ArielleZhang/ESC204_PraxisIII_The_wandering_sheep/Design Pitch Artefacts/Design Consideration and Prototyping Artefacts/Phase B/Database + UI/grassresized.png

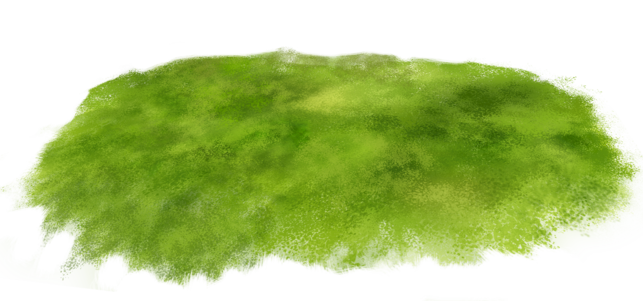
Design Pitch Artefacts/Design Consideration and Prototyping Artefacts/Phase B/Database + UI/grassresized.png
