ArielleZhang/ESC204_PraxisIII_The_wandering_sheep/Design Milestones/Prototype/Physical Collar Design/DesignOutline.docx

Belt

1. Use vinyl for the belt, this is waterproof and durable, an ideal material for sheep collar.(remember to sandpaper the edge to avoid sharp edges)
2. Belt buckles, 3D print two square rings. (from reference design, this is easier to use compared to watch style belts with complicated buckles)

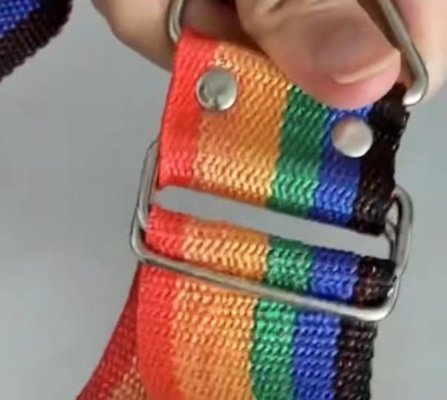
[picture p41: figure]

3. Belt case connections: still need to think about how to attach the belts onto the case. There are two ear rings on the case.

Case:

1. Size is 72mmx62mmx20mm right now. (Could we make it even smaller?)
2. Need to hold the Arduino and the Bluefruit in place, no movements even when shaking.
  a. Add a middle layer for the Bluefruit, need to drill holes and screw it on the plate.
3. Waterproof/dustproof mechanism.
