ArielleZhang/ESC204_PraxisIII_The_wandering_sheep/Design Milestones/Phase A/To Do.docx

- Executive summary – write when finished
- Finish up opportunity statement (confusing) - write when finished
- Background (Ethan was working on this)
- Reference design (fencing) (Ethan)
- Team value proposition - Edwin
- Individual requirements write up (make it into paragraph form, follow cost-efficiency format)
- Emre's team description
- Everything design related:
  - Finalizing the two designs (Arielle&Tab&Edwin work on one design, Emre&Ethan work on the other design)
  - Design descriptions
    - Thermal
    - Image recognition
  - Prototype for thermal (or whatever we’re choosing)
  - why the second one didn’t work
- Project management plan summary (Arielle)
