ArielleZhang/ESC204_PraxisIII_The_wandering_sheep/Design Pitch Artefacts/Project Management Artefacts/3. Communication Protocol.docx

Communication Protocol Be responsive: - Keep up with messages in group chats (discord) regularly and reply ASAP Show punctuality: - Don’t be late, have time strictly reserved for Praxis! Be communicative: - Come prepared to all meetings - Speak up/ don’t be shy, no one is judging - Contribute ideas to the group Be attentive and respectful: - Keep an open mind to everyone's opinions - Try to think in each other's perspectives
