ArielleZhang/ESC204_PraxisIII_The_wandering_sheep/Housekeeping/GSU_Interaction/GSU Initial Contact.docx

Initial contact with the GSU student

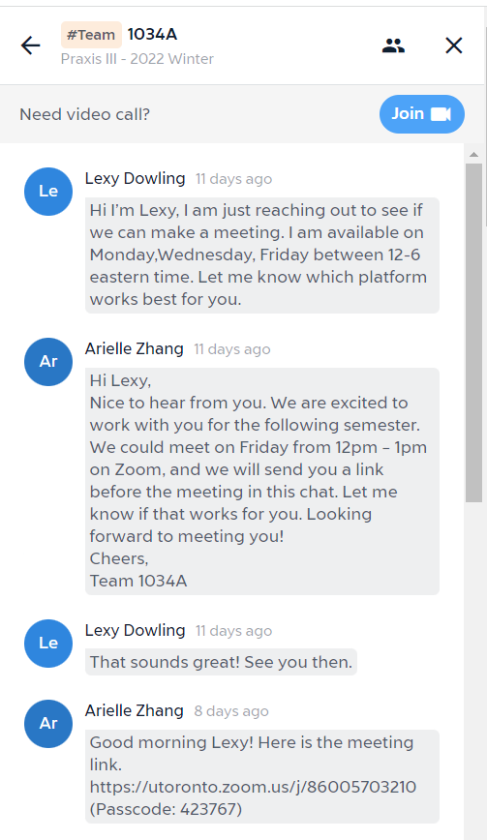
[picture p56: figure]
