ArielleZhang/ESC204_PraxisIII_The_wandering_sheep/Housekeeping/GSU_Interaction/GSU meeting confirmation.docx

GSU Meeting Confirmation Email

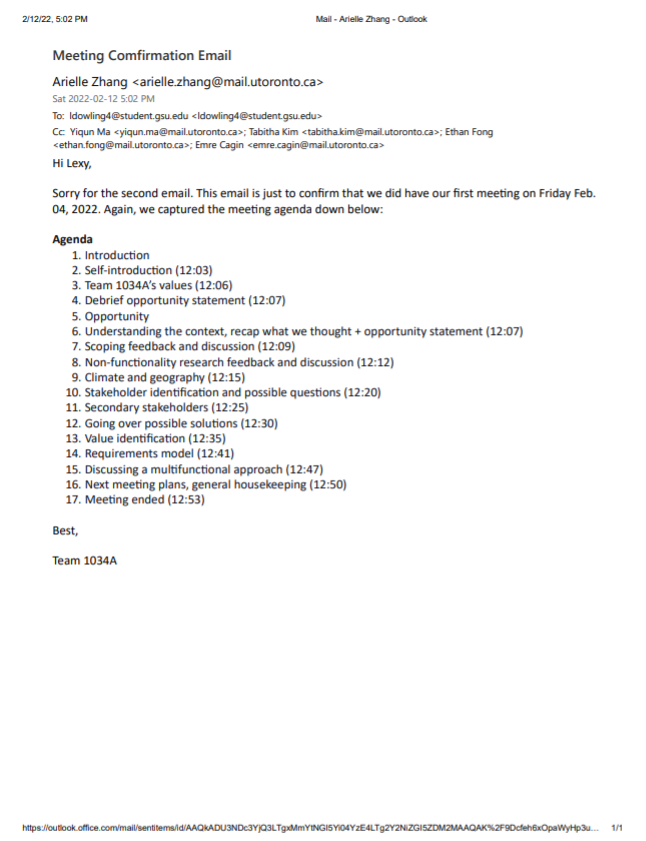
[picture p57: figure]
