ArielleZhang/ESC204_PraxisIII_The_wandering_sheep/Research/Yiqn_Research/Solution.docx

Edwin Research

Possible solution

Drone Method

The drone is efficient and easy to control, the controller is designed to be as much easy as we can. The drone is small and fast that can fly everywhere, sheep can only wander off around 5km, so using drones to find where they are is much easier for owners to drive cars to each one’s house. Drones can also be used as monitors, both check the actions of shepherds and chase for missing sheep at the first second they wander off, this increases the efficiency for the owner to find back their sheep since they know exactly where to go.

The drone can be also used to monitor situations of sheep in the crowd, for example, the new birth is produced, the owner can know the message immediately as they can see all the scenes of his sheep. Thermal imaging is another key feature to monitor the health of sheep.

Sensors can be used to identify belong of the sheep, the paint on sheep will affect the wool production, so I think an induction device placed on sheep’s ear that can produce certain signals can solve the problem of identifying sheep. All families on this land can select their signals for drones to identify the owner of lost sheep.

Ease of learning

an individual’s prediction of how easy it will be to acquire and retain certain items of information, given before any attempt is made to do so. In tests of learning and memory, participants’ pretest ease-of-learning judgments tend to be only weakly correlated with their performance on the test. Like the feeling of knowing (https://dictionary.apa.org/feeling-of-knowing), ease-of-learning judgments are an important aspect of metacognition (https://dictionary.apa.org/metacognition). Compare retrospective confidence judgment (https://dictionary.apa.org/retrospective-confidence-judgment).

The two methods of drone and tracker are both easy for them to learn, it is easy to put the tracker on sheep’s ears and use their phone to track their locations. Also it will only take a short time to learn how to use the drones
