ArielleZhang/ESC204_PraxisIII_The_wandering_sheep/Design Pitch Artefacts/Project Management Artefacts/ESC204S-Course-Schedule-Gantt-Chart-2022-STUDENT-COPY.xlsx

Sheet: Schedule Gantt - Mostly Phase A
Month | January |  |  | February |  |  |  | March |  |  |  | April
Week | WK 1 | WK 2 | WK 3 | WK 4 | WK 5 | WK 6 | WK 7 | WK 8 | WK 9 | WK 10 | WK 11 | WK 12 | WK 13 | WK 14 | Exam Period
Dates | 01/10 - 01/16 | 01/17 - 01/23 | 01/24 - 01/30 | 01/31 - 02/06 | 02/07 - 02/13 | 02/14 - 02/20 | 02/21 - 02/27 | 02/28 - 03/06 | 03/07 - 03/13 | 03/14 - 03/20 | 03/21 - 03/27 | 03/28 - 04/03 | 04/04 - 04/10 | 04/11 - 04/16 | 04/19 - 04/23 | 04/24 - 04/30
Deliverable / Activity
Meeting |  |  |  |  |  |  |  |  | Meeting 1 | No Merting, update through DC
Studios |  |  |  |  |  |  |  |  | Studio A: 1. TELS 2. Prototype, checkin with the team resiponsibility tracker 3. Widget Lab 3 order | Studio B: 1. continue debugging GPS 2. finish lab 3 code+cad 3. procurement Studio A: 1. Start on prototype 2. Budget upadte 3. start on widet lab 3 4. lab3 report | Studio A: 1. TELS 2.Prototype 3. Requirements + testing protocol | Studio A 1. Follower sheep assembling 2. Backend read from serial monitor, UI 3. Brochure 4. Testing protocol | Presentation on Friday | Documeny + demo due
Design Pitch |  |  |  |  |  |  |  |  | 2021-03-07 |  |  |  |  | 2022-04-17
PMP Review |  |  |  |  |  |  |  |  |  | Studio B
Prototyping Check-In |  |  |  |  |  |  |  |  | 2021-03-07 |  | Studio B
Design Pitch Brochure |  |  |  |  |  |  |  |  | 2021-03-07 |  |  | 2022-04-03
Deign Pitch Presentation + Recordings |  |  |  |  |  |  |  |  | 2021-03-07 |  |  |  | Studio A+B
Design Pitch Document & Prototype Demo Recordings |  |  |  |  |  |  |  |  | 2021-03-07 |  |  |  |  | 2021-04-17
GSU Peer Interactions
GSU Peer Interactions - Phase A - Synchronous Meeting (https://q.utoronto.ca/courses/244355/assignments/806370) |  |  |  | 2021-01-31 | 2022-02-13
GSU Peer Interactions - Phase B - Asynchronous Feedback |  |  |  |  |  |  |  | 2021-03-06 | 2022-03-13
Reflections (Individual Designer's Identity)
Reflection 1 - Designer's Empathy (https://q.utoronto.ca/courses/244355/assignments/794634) | 2022-01-13 | 2021-01-23
Reflection 2 - Designer's Bias |  |  |  |  |  |  |  |  | 2022-03-08 | 2022-03-20
Refleciton 3 |  |  |  |  |  |  |  |  |  |  |  |  | 2021-04-04 |  | 2021-04-23
TELS
TELS 1 |  |  |  |  |  |  |  | 2022-03-01 | 2021-03-13
TELS 2 |  |  |  |  |  |  |  |  |  |  |  |  |  | TBD | 2021-04-23
Team Video Recordings
Team Meeting Video Recording - Phase A (https://q.utoronto.ca/courses/244355/assignments/820351) |  | Studio A |  |  |  |  |  | 2021-03-06
Team Meeting Video Recording - Phase B |  |  |  |  |  |  |  |  | 2021-03-07 |  |  |  |  |  |  | 2021-04-30
Widget Skill Building
Lab 1 - Basic Systems Prototyping (pairs) (https://q.utoronto.ca/courses/244355/assignments/797602) | 2022-01-16 |  |  | 2022-02-06
Lab 2 - Intermediate Systems Prototyping (teams) (https://q.utoronto.ca/courses/244355/assignments/816949) |  |  |  |  | 2022-02-07 |  |  |  | 2022-03-09
Lab 3 - Advanced Systems Prototyping (teams) |  |  |  |  |  |  |  | 2022-03-04 |  |  | 2022-03-23
Design Proposal Process (https://q.utoronto.ca/courses/244355/assignments/818248) | 2022-01-12 |  |  |  |  | 2021-02-20
Project Framing |  |  | 2022-01-24 | Studio A |  | 2021-02-20
Design Considerations |  |  | 2022-01-24 |  | Studio A | 2021-02-20
Project Management Plan |  | Studio A | Studio A | Studio A | Studio A | 2021-02-20
Course Introduction & Setup
Survey & Team Formation (https://q.utoronto.ca/courses/244355/assignments/793460) | 01/12-01/15
Legend
begin / assigned | M/DD | Studio A or B
in-progress
submission due 23:59 ET (unless otherwise specified) | M/DD
informal (in-studio) check-in on current state | Studio A or B
submission not assessed (used for course improvement) | M/DD
deadline for external partners (nothing to submit) | M/DD

Sheet: Weekly Timetable
Time | Monday | Tuesday |  |  |  |  | Wednesday |  | Thursday |  |  |  |  |  | Friday
9:00:00 |  |  |  |  |  |  |  |  |  |  | TUT0109 | TUT0110 | TUT0107 | TUT0108 | PRA0103 | PRA0104 | PRA0109 | PRA0110 | PRA0107 | TUT0108
10:00:00 |  |  |  |  |  |  |  |  | PRA0111 | PRA0112
11:00:00
12:00:00 |  | PHILIP IN CAPSTONE
13:00:00 |  |  |  |  |  |  | TUT0111 | TUT0112 | PRA0101 | PRA0102
14:00:00 |  |  |  |  |  |  |  |  |  |  | PRA0105 | PRA0106 |  |  | LEC
15:00:00 |  |  | TUT0101 | TUT0102 | TUT0105 | TUT0106 | TUT0103 | TUT0104 | PHILIP IN |  |  |  | CAPSTONE
16:00:00 | LEC
17:00:00 |  | LEC
18:00:00 |  | TUT0113 |  |  |  |  |  |  | PRA0113
19:00:00
20:00:00
