ArielleZhang/ESC204_PraxisIII_The_wandering_sheep/Design Milestones/Prototype/Back End/First Version/shaun.png

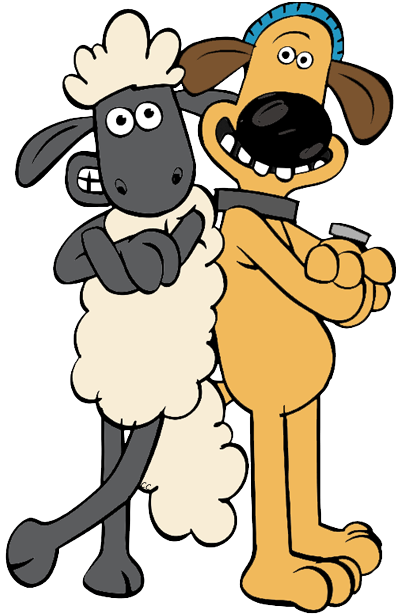
Design Milestones/Prototype/Back End/First Version/shaun.png
