ArielleZhang/ESC204_PraxisIII_The_wandering_sheep/Design Milestones/Prototype/Conceptual Design.png

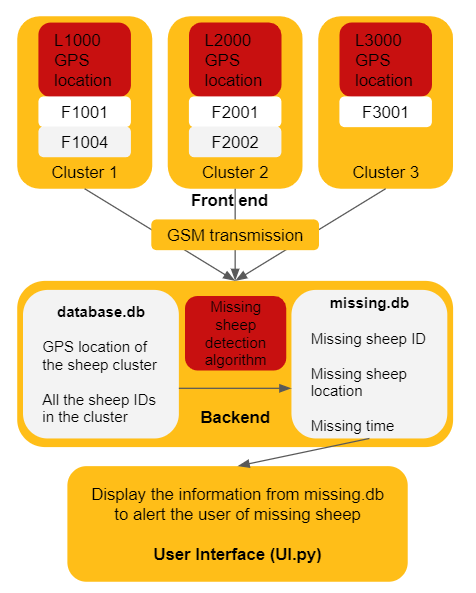
Design Milestones/Prototype/Conceptual Design.png
