ArielleZhang/ESC204_PraxisIII_The_wandering_sheep/Design Milestones/Prototype/green design concept.png

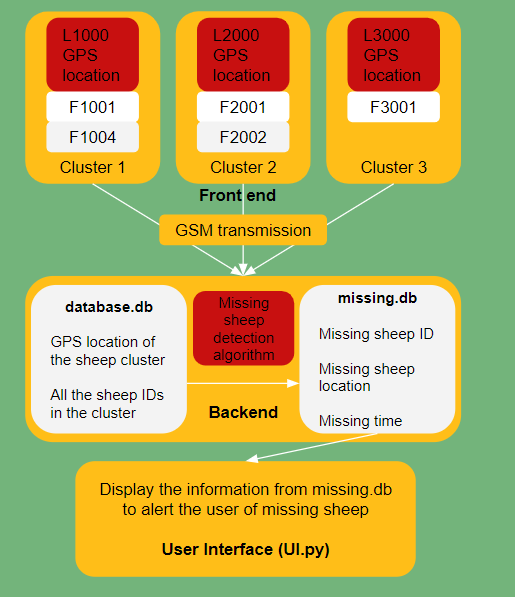
Design Milestones/Prototype/green design concept.png
