ArielleZhang/ESC204_PraxisIII_The_wandering_sheep/Design Milestones/Prototype/Physical Collar Design/Collar_Design_Version1.png

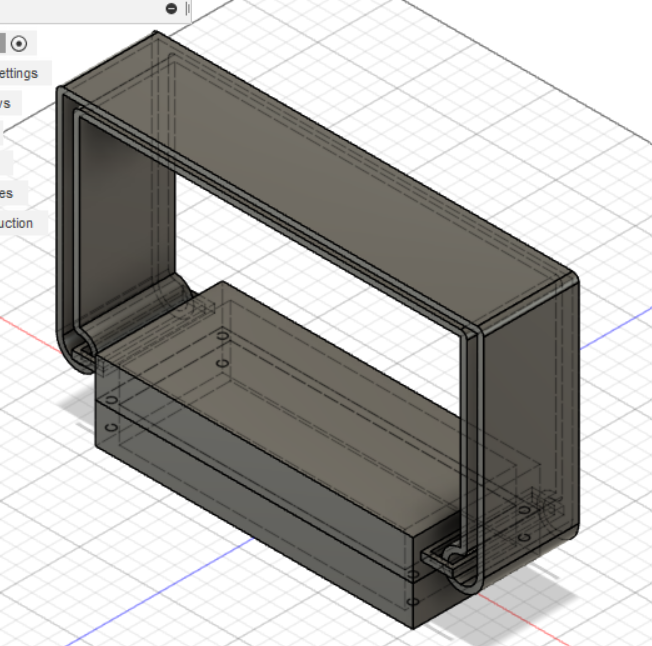
Design Milestones/Prototype/Physical Collar Design/Collar_Design_Version1.png
