ArielleZhang/ESC204_PraxisIII_The_wandering_sheep/Design Milestones/Prototype/Testing Protocols/Frontend Electrical System/Frontend testing against requirements.docx

Safety – operating voltage and signal strengths

Should not affect sheep ->
