ArielleZhang/ESC204_PraxisIII_The_wandering_sheep/Design Pitch Artefacts/Design Consideration and Prototyping Artefacts/Phase A/Results of our initial convergence.jpg

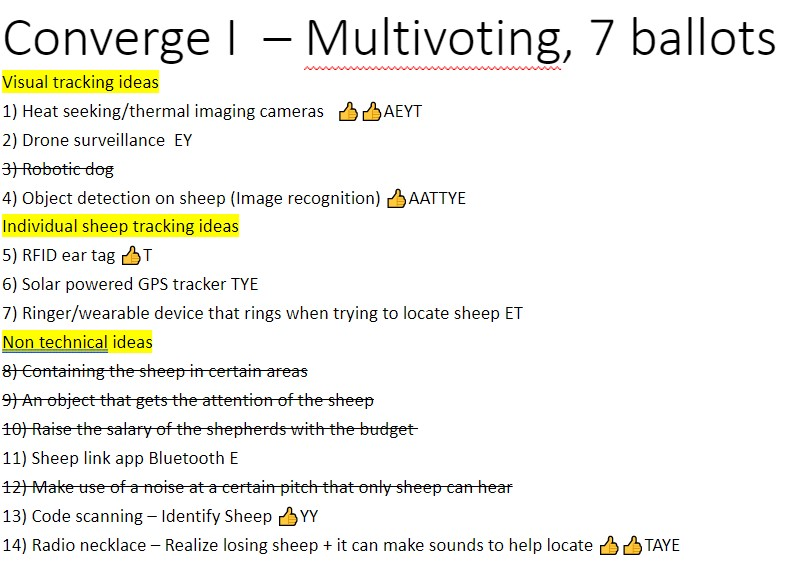
Design Pitch Artefacts/Design Consideration and Prototyping Artefacts/Phase A/Results of our initial convergence.jpg
